Jangmyun/Full-Custom-Keyboard/img/pcb/pcb14.png

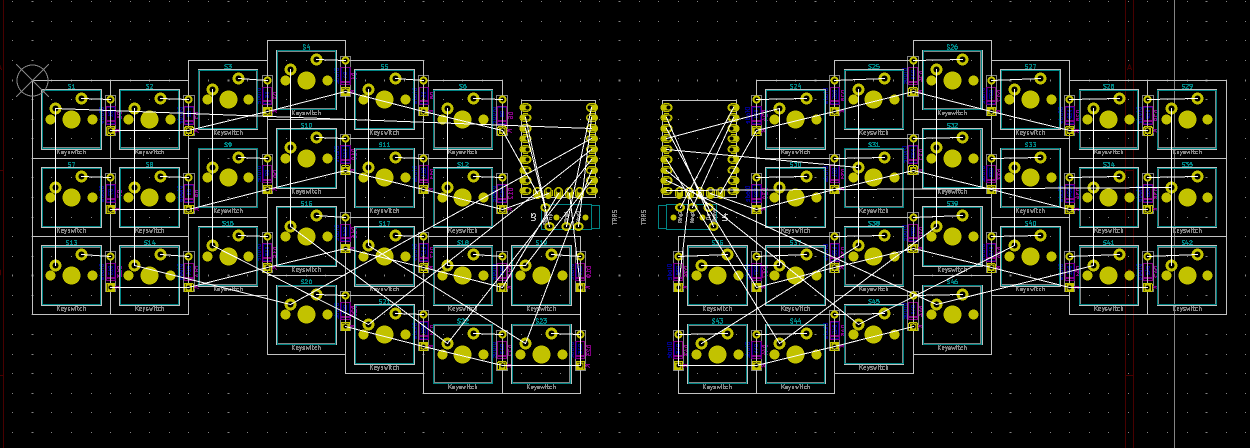
img/pcb/pcb14.png
